zauberwild/Arduino_Controller/cad/media/1ec1cc6d-fcb6-425c-a1da-dc70da69a3c4.TIFF

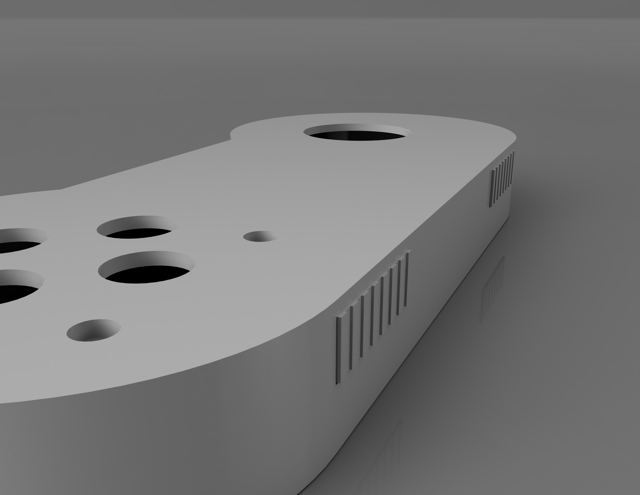
cad/media/1ec1cc6d-fcb6-425c-a1da-dc70da69a3c4.TIFF
