zauberwild/Arduino_Controller/cad/media/b1062258-fd47-4a83-8459-486fa421ad4d.PNG

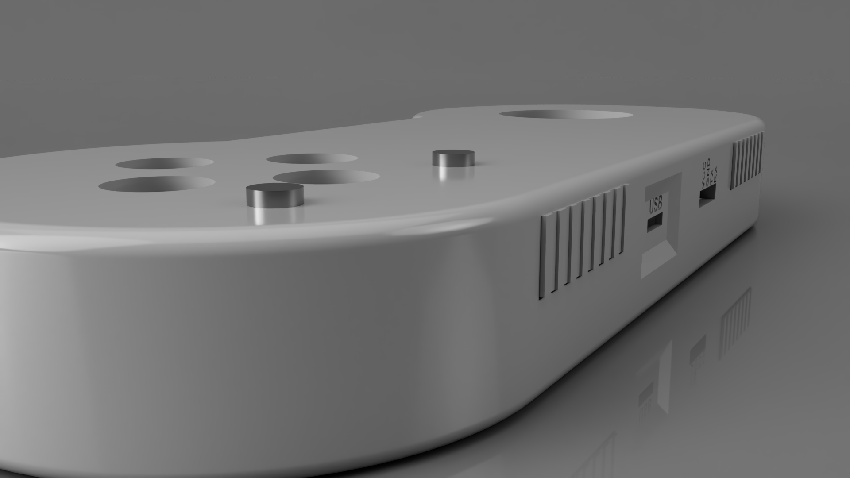
cad/media/b1062258-fd47-4a83-8459-486fa421ad4d.PNG
