zauberwild/Arduino_Controller/cad/media/Controller v18.png

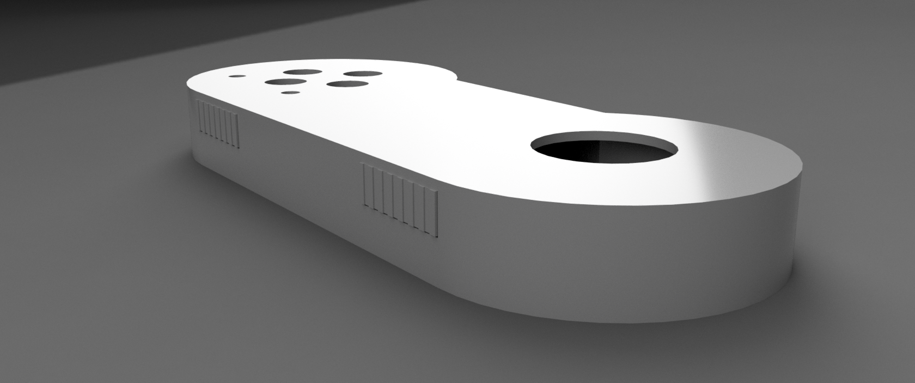
cad/media/Controller v18.png
