zauberwild/Arduino_Controller/cad/media/Controller_2021-Feb-25_02-02-42PM-000_CustomizedView17104366932.png

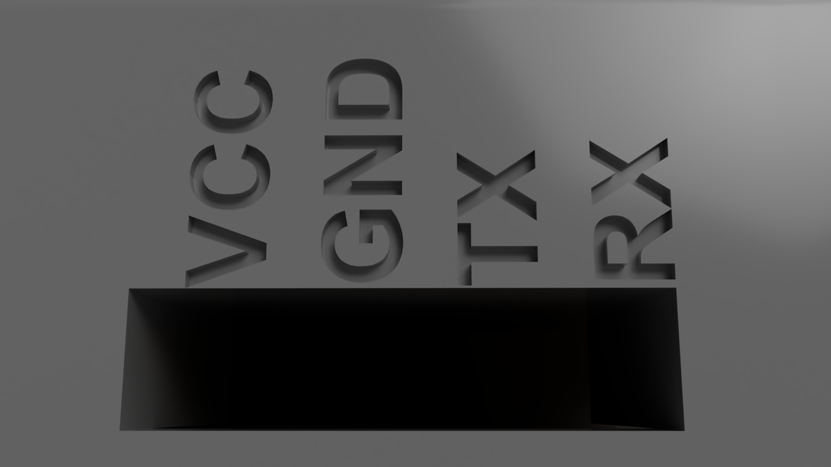
cad/media/Controller_2021-Feb-25_02-02-42PM-000_CustomizedView17104366932.png
