zauberwild/Arduino_Controller/cad/media/Controller_2021-Mar-03_04-40-33PM-000_CustomizedView20378346485.png

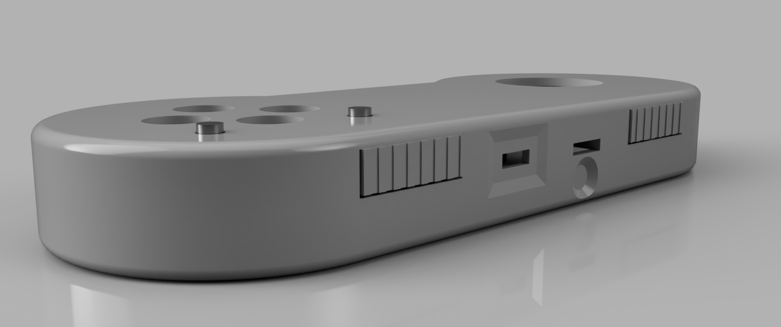
cad/media/Controller_2021-Mar-03_04-40-33PM-000_CustomizedView20378346485.png
