zauberwild/Arduino_Controller/media/images/notes (2).jpg

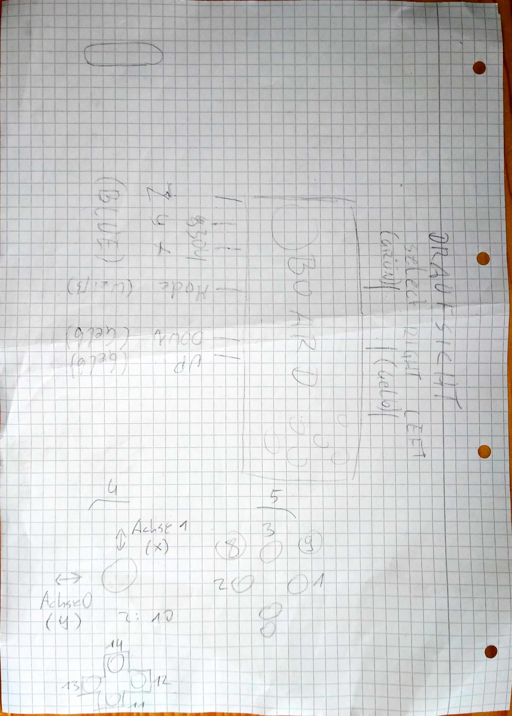
media/images/notes (2).jpg
